fengxueem/Turtle-Snake-Flashlight/Documents for EXPO2015/123dx/turtle-origin.jpg

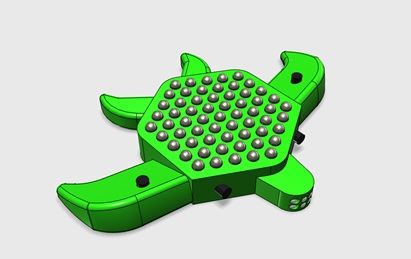
Documents for EXPO2015/123dx/turtle-origin.jpg
