fengxueem/Turtle-Snake-Flashlight/Documents for EXPO2015/circuit diagram/charlieplexing-page-001.jpg

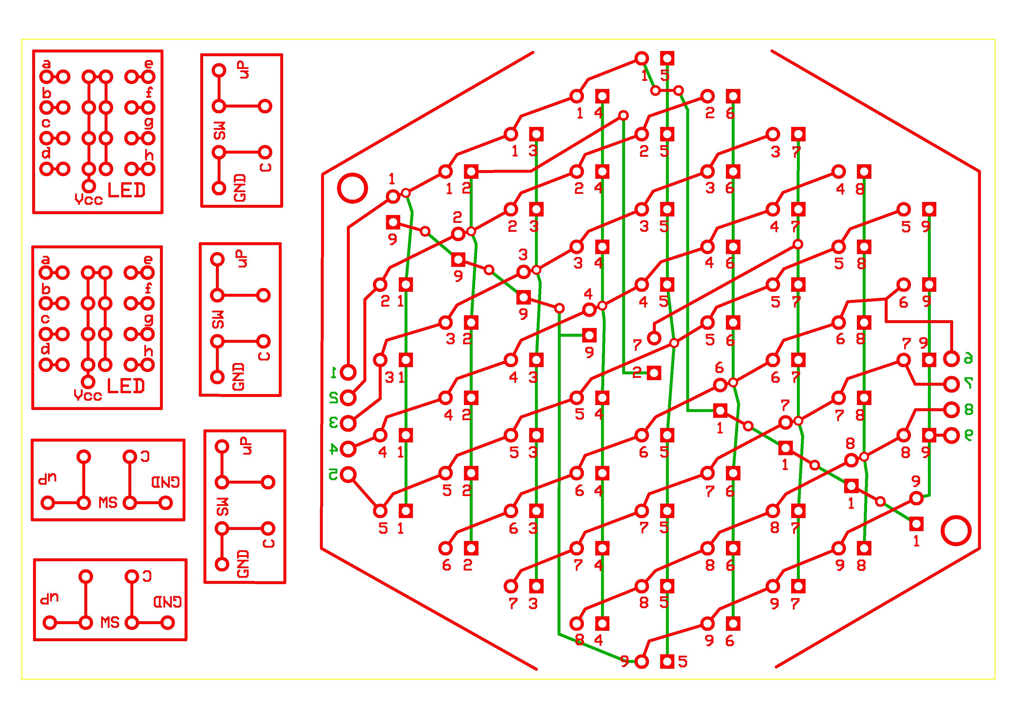
Documents for EXPO2015/circuit diagram/charlieplexing-page-001.jpg
