fengxueem/Turtle-Snake-Flashlight/Documents for EXPO2015/circuit diagram/mainboard.jpg

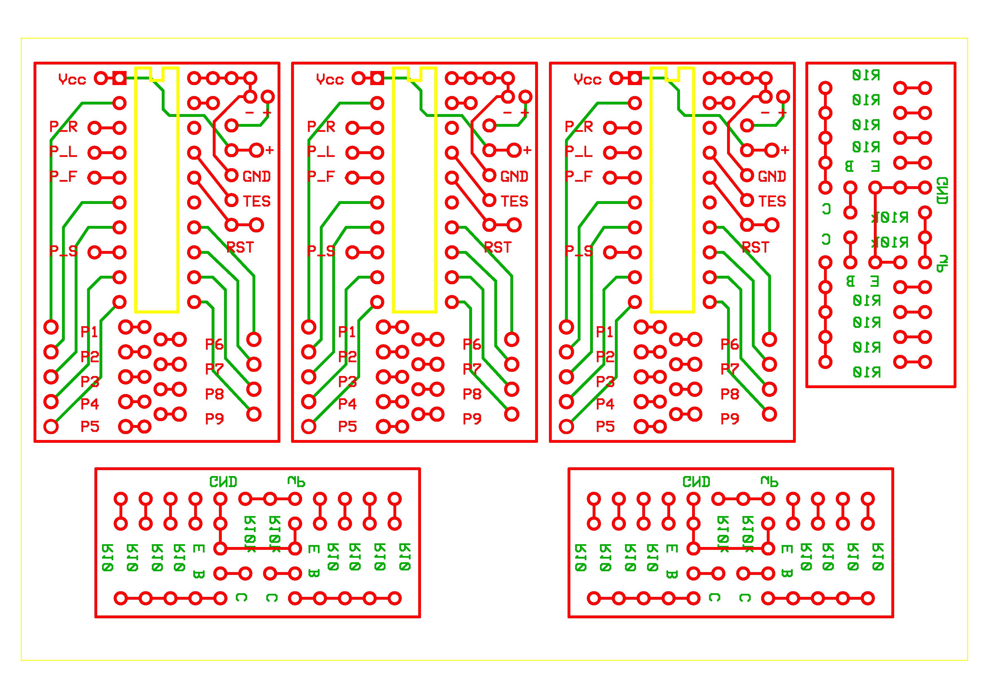
Documents for EXPO2015/circuit diagram/mainboard.jpg
