fengxueem/Turtle-Snake-Flashlight/Documents for EXPO2015/early sketch/LED matrix coordinates1.jpg

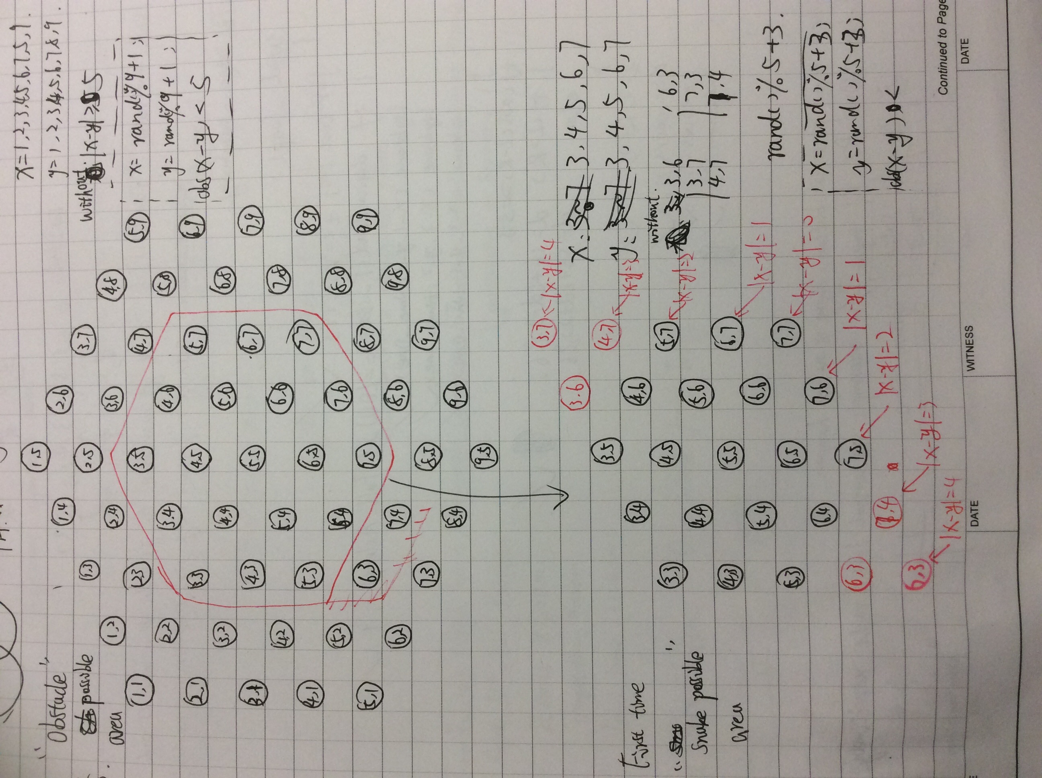
Documents for EXPO2015/early sketch/LED matrix coordinates1.jpg
