fengxueem/Turtle-Snake-Flashlight/Documents for EXPO2015/early sketch/LED matrix coordinates 2.jpg

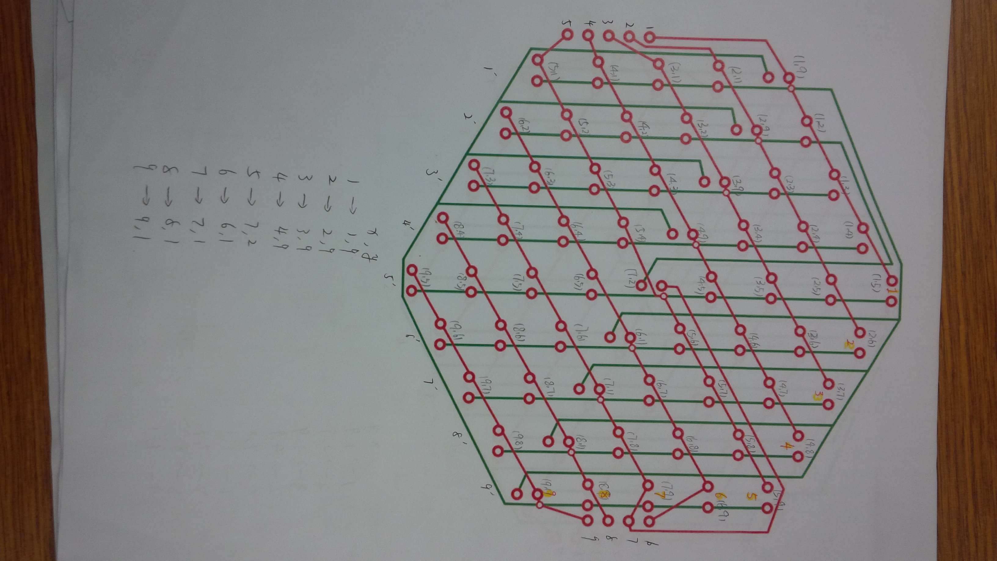
Documents for EXPO2015/early sketch/LED matrix coordinates 2.jpg
