fengxueem/Turtle-Snake-Flashlight/Documents for EXPO2015/early sketch/Oldest Appearance sketch.jpg

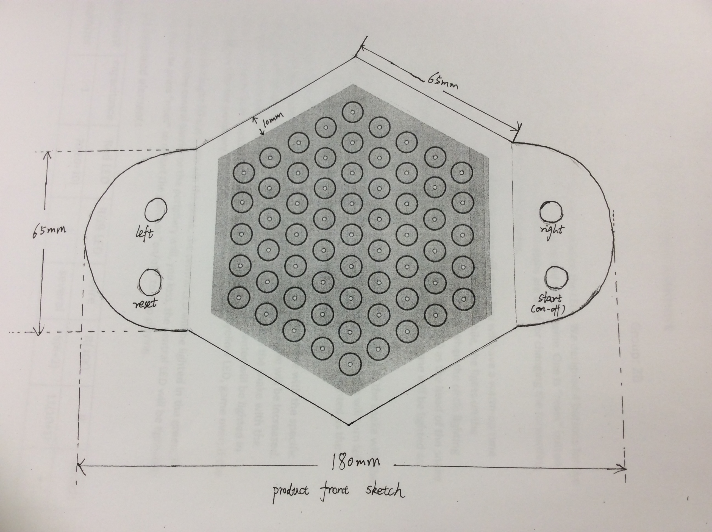
Documents for EXPO2015/early sketch/Oldest Appearance sketch.jpg
