fengxueem/Turtle-Snake-Flashlight/Documents for EXPO2015/early sketch/PCB LED Locations.JPG

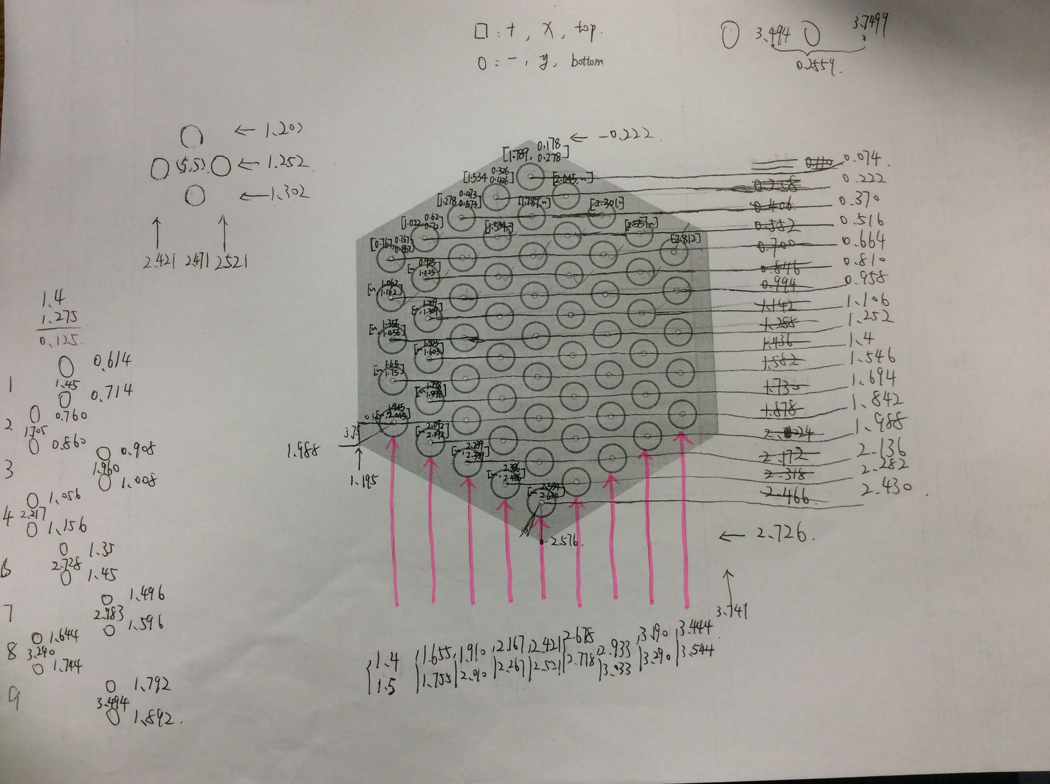
Documents for EXPO2015/early sketch/PCB LED Locations.JPG
