fengxueem/Turtle-Snake-Flashlight/Documents for EXPO2015/photo of prototype/IMG_20150415_145007.jpg

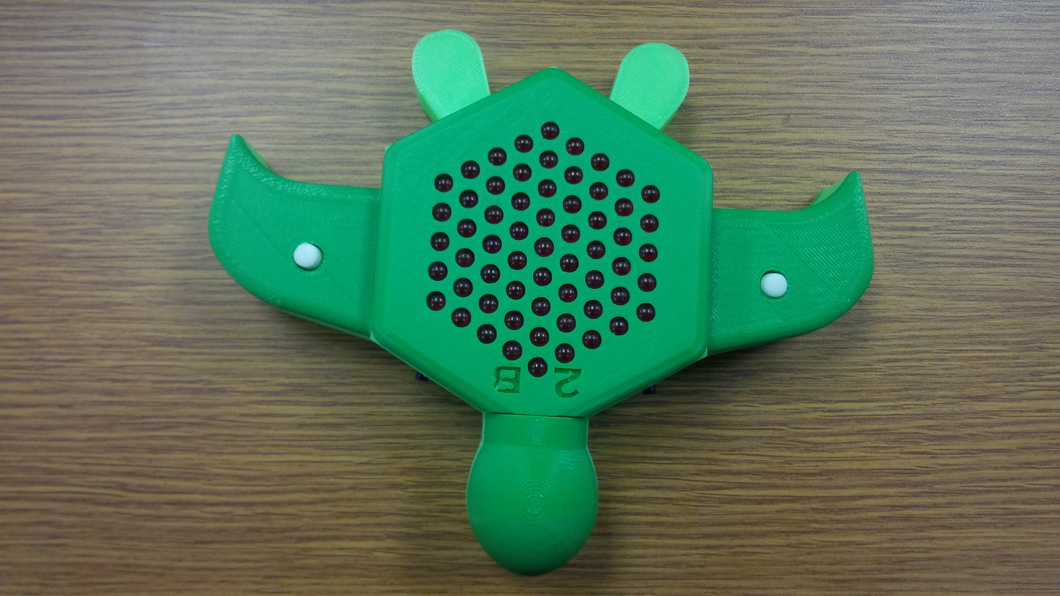
Documents for EXPO2015/photo of prototype/IMG_20150415_145007.jpg
