fengxueem/Turtle-Snake-Flashlight/Documents for EXPO2015/team photo/Hard Working1.jpeg

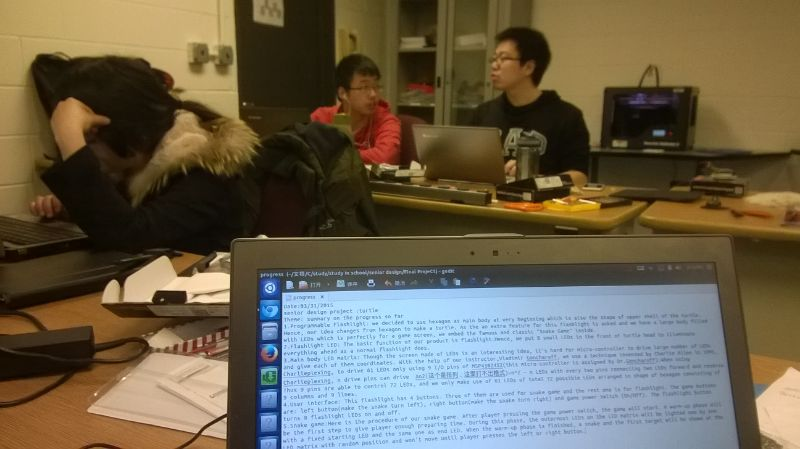
Documents for EXPO2015/team photo/Hard Working1.jpeg
