fengxueem/Turtle-Snake-Flashlight/Documents for EXPO2015/team photo/Hard working2.jpeg

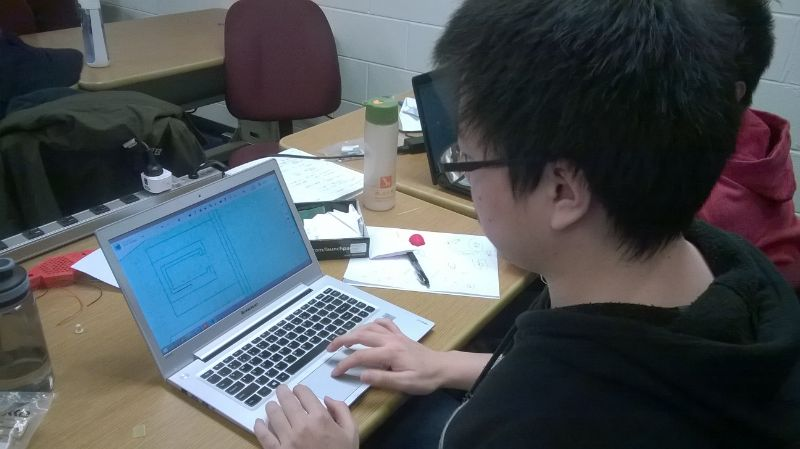
Documents for EXPO2015/team photo/Hard working2.jpeg
