fengxueem/Turtle-Snake-Flashlight/Documents for EXPO2015/team photo/Hard working3.jpeg

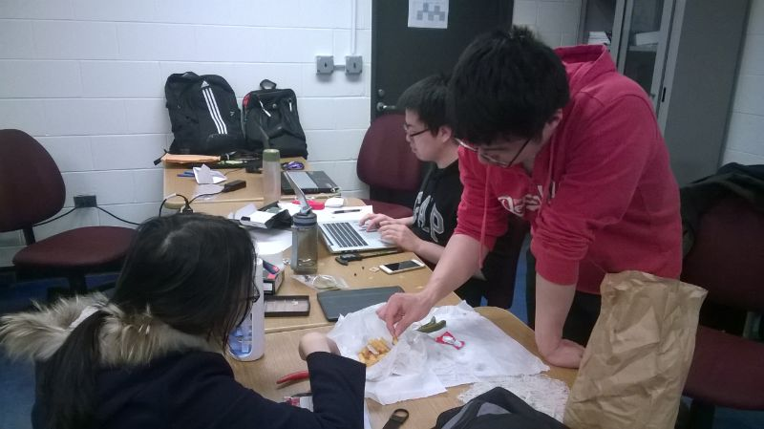
Documents for EXPO2015/team photo/Hard working3.jpeg
