fengxueem/Turtle-Snake-Flashlight/Documents for EXPO2015/team photo/Hard working4.jpeg

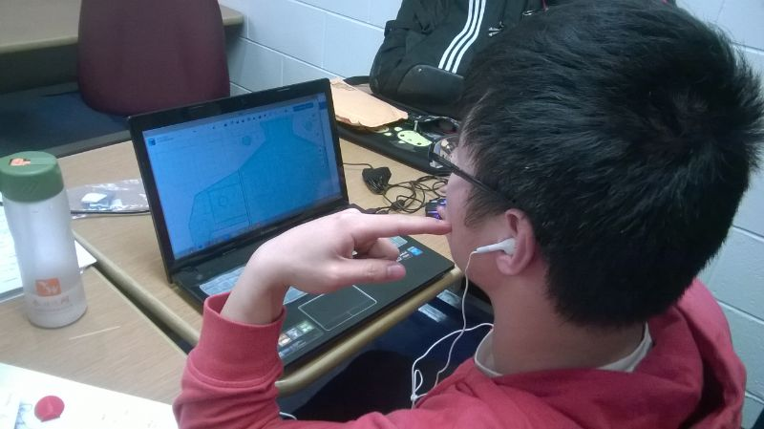
Documents for EXPO2015/team photo/Hard working4.jpeg
