fengxueem/Turtle-Snake-Flashlight/Documents for EXPO2015/team photo/Team Photo.jpg

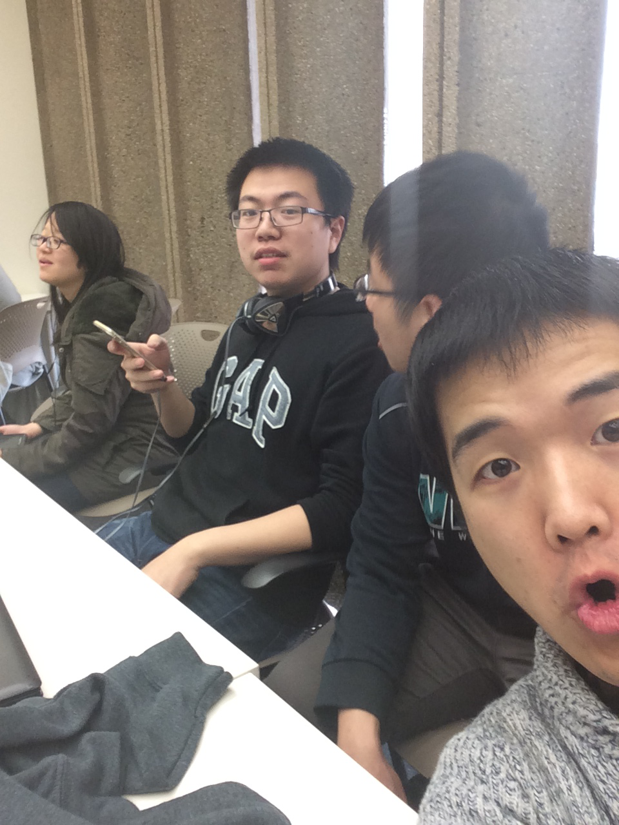
Documents for EXPO2015/team photo/Team Photo.jpg
