fengxueem/Turtle-Snake-Flashlight/Ideas/MayFlower/snowflake.jpg

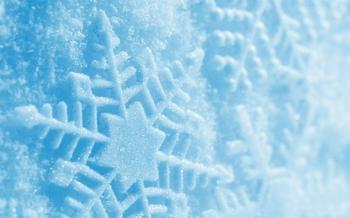
Ideas/MayFlower/snowflake.jpg
